MrRyabena/ClimateStation/src/ClimateStation/shs_ClimateStationStorage.cpp

#include "shs_ClimateStationStorage.h"


shs::ClimateStationStorage::ClimateStationStorage(const uint8_t SD_CS)
    : m_SD_CS(SD_CS)
{}


void shs::ClimateStationStorage::start()
{
    beginSD();    // Reading the config, if it exists. If not, then save the default values.
}


void shs::ClimateStationStorage::tick()
{
    if (m_status != Status::CARD_OK) beginSD();
}


void shs::ClimateStationStorage::stop()
{}


bool shs::ClimateStationStorage::saveNextData(const shs::ClimateStationData& data)
{
    if (m_status != Status::CARD_OK) return false;

    File file = SD.open(m_getDateFileName(data.time), FILE_APPEND);
    if (!file) { return false; }

    file.write(reinterpret_cast<const uint8_t*>(&data), sizeof(data));
    file.close();

    return true;
}


bool shs::ClimateStationStorage::beginSD()
{
    bool result = SD.begin(m_SD_CS);

    if (!result)
    {
        uint8_t cardType = SD.cardType();
        switch (cardType)
        {
            case CARD_NONE: m_status = Status::CARD_NONE; break;
            case CARD_MMC: [[fallthrough]];
            case CARD_SD: [[fallthrough]];
            case CARD_SDHC: [[fallthrough]];
            default: m_status = Status::CARD_UNKNOWN; break;
        }

        return false;
    }

    m_status = Status::CARD_OK;

    m_checkAndCreateDirectory(m_STORAGE_DIR);

    getConfig(cs_config);

    return true;
}


bool shs::ClimateStationStorage::save_TFT_calData(const uint16_t* calData)
{
    m_checkAndCreateDirectory(m_TFT_DATA_DIR);
    auto file = SD.open(shs::t::shs_string_t(m_TFT_DATA_DIR) + F("TOUCH_calibration_data.shsf"), FILE_WRITE);

    if (!file) return false;

    auto bytes = file.write(reinterpret_cast<const uint8_t*>(calData), m_TFT_TOUCH_CALIBRATION_DATA_SIZE * 2);
    file.close();

    return bytes == m_TFT_TOUCH_CALIBRATION_DATA_SIZE * 2;
}


bool shs::ClimateStationStorage::get_TFT_calData(uint16_t* calData)
{
    auto file = SD.open(shs::t::shs_string_t(m_TFT_DATA_DIR) + F("TOUCH_calibration_data.shsf"), FILE_READ);

    if (!file) return false;

    auto bytes = file.read(reinterpret_cast<uint8_t*>(calData), m_TFT_TOUCH_CALIBRATION_DATA_SIZE * 2);
    file.close();

    return bytes == m_TFT_TOUCH_CALIBRATION_DATA_SIZE * 2;
}


bool shs::ClimateStationStorage::saveConfig(const shs::ClimateStationConfig& config)
{
    m_checkAndCreateDirectory(m_CONFIG_FILE);
    return writeFile(shs::t::shs_string_t(m_CONFIG_FILE) + "config.shsf", reinterpret_cast<const uint8_t*>(&config), sizeof(config));
}


bool shs::ClimateStationStorage::getConfig(shs::ClimateStationConfig& config)
{
    if (SD.exists(shs::t::shs_string_t(m_CONFIG_FILE) + "config.shsf"))
    {
        // shs::ClimateStationConfig conf;
        readFile(shs::t::shs_string_t(m_CONFIG_FILE) + "config.shsf", reinterpret_cast<uint8_t*>(&config), sizeof(config));

        // if (conf.config_version == config.config_version)
        // {
        //     config = conf;
        //     return true;
        // }
    }

    saveConfig(config);
    return false;
}


size_t shs::ClimateStationStorage::readFile(const shs::t::shs_string_t& fname, uint8_t* buf, const size_t size)
{
    auto file = SD.open(fname, FILE_READ);
    if (!file) return 0;

    auto bytes = file.read(buf, size);
    file.close();

    return bytes;
}


size_t shs::ClimateStationStorage::writeFile(const shs::t::shs_string_t& fname, const uint8_t* buf, const size_t size)
{
    m_checkAndCreateDirectory(fname.substring(0, fname.lastIndexOf('/')));
    auto file = SD.open(fname, FILE_WRITE);
    if (!file) return 0;

    auto bytes = file.write(buf, size);
    file.close();

    return bytes;
}



shs::t::shs_string_t shs::ClimateStationStorage::m_getDateFileName(const shs::t::shs_time_t time)
{
    Datime datime(time);
    char buf[3]{};

    shs::t::shs_string_t file_name = m_STORAGE_DIR;
    file_name.reserve(4 + 2 + 2);

    file_name += datime.year;

    m_z_filled(datime.month, buf);
    file_name += buf;

    m_z_filled(datime.day, buf);
    file_name += buf;

    file_name += F(".shsf");

    return file_name;
}


void shs::ClimateStationStorage::m_checkAndCreateDirectory(const shs::t::shs_string_t& dir_name)
{
    auto i = dir_name.indexOf('/', 1);
    auto sub_dir = dir_name.substring(0, i);
    sub_dir.reserve(dir_name.length());

    if (!SD.exists(sub_dir))
    {
        SD.mkdir(sub_dir);
    }


    for (i; i < dir_name.length() - 1; )
    {
        auto new_i = dir_name.indexOf('/', i + 1);
        if (new_i == -1) new_i = dir_name.length() - 1;
        sub_dir += dir_name.substring(i, new_i);
        i = new_i;

        if (!SD.exists(sub_dir))
        {
            if (SD.mkdir(sub_dir));
        }
    }


}


void shs::ClimateStationStorage::m_z_filled(const uint8_t value, char* buf)
{
    buf[0] = '0' + value / 10;
    buf[1] = '0' + value % 10;
}
