MrRyabena/ClimateStation/src/ClimateStation/ClimateStationGUIcore.h

#pragma once

#include "GUIcore/Widget.h"
#include "GUIcore/Widget.cpp"
#include "GUIcore/RectWidget.h"
#include "GUIcore/RectWidget.cpp"
#include "GUIcore/utils.h"
#include "GUIcore/shs_ThemeColors.h"
#include "GUIcore/Label.h"
#include "GUIcore/Label.cpp"
#include "GUIcore/IndicatorWidget.h"
#include "GUIcore/IndicatorWidget.cpp"
