MrRyabena/ClimateStation/src/ClimateStation/settings.h

#pragma once

// #define DEBUG

#define CLIMATE_STATION_ESP32_VERSION "1.0.6"

static constexpr auto LEDS_NUM = 9 * 5;
static constexpr auto LEDS_PIN = 16;

static constexpr auto SD_CS = 3;
static constexpr auto SD_MOSI = 23;
static constexpr auto SD_MISO = 34;
static constexpr auto SD_SCK = 18;
